michaelfsb/cea_sadv_cape_bbb/componetes/MPU-6050/3D/MPU-6050.stp

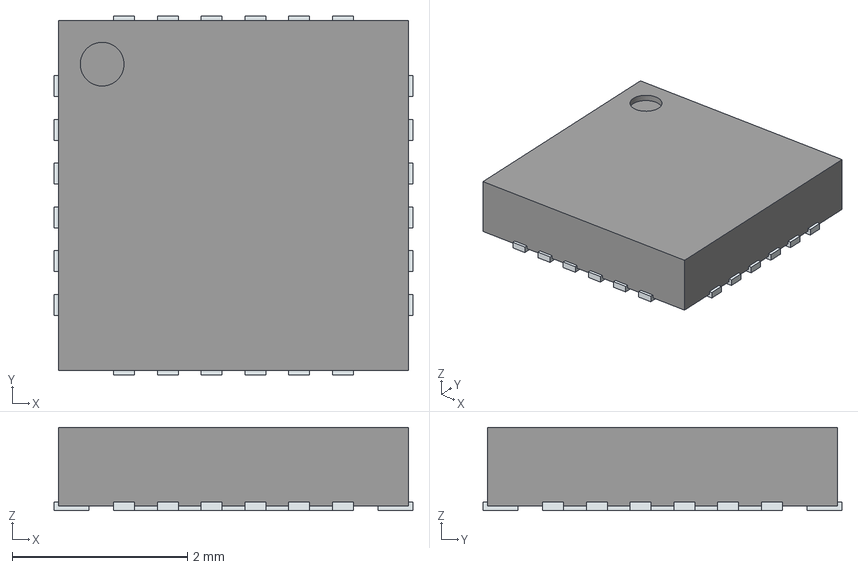
[picture p15: CAD file, 2018-07-10]
componetes/MPU-6050/3D/MPU-6050.stp
4.10 x 4.10 x 0.95 mm
ThermalPin
PinsArrayLR
PinsArrayTB
