michaelfsb/cea_sadv_cape_bbb/componetes/MPU-6500/3D/mpu6500.STEP

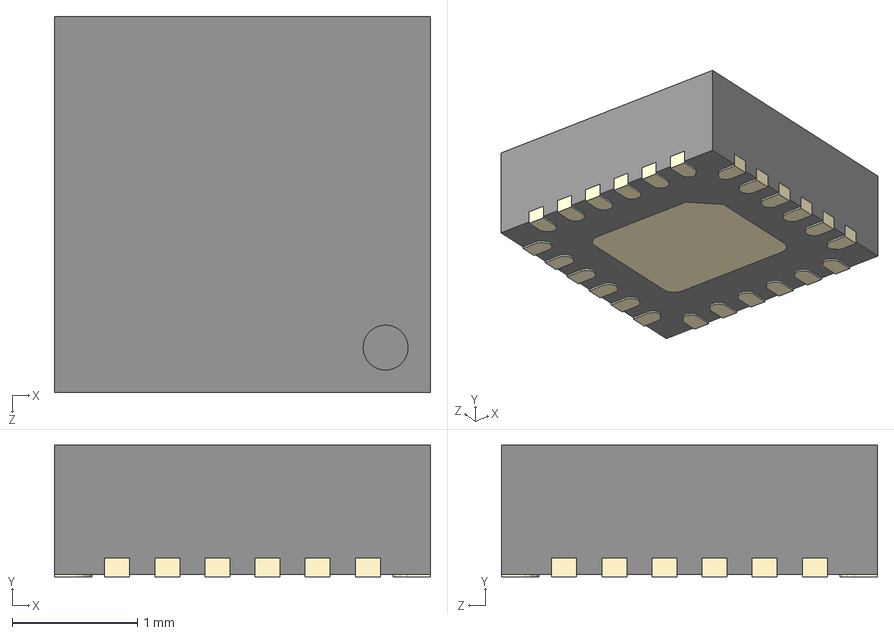
[picture p16: CAD file, 2018-08-18]
componetes/MPU-6500/3D/mpu6500.STEP
3.00 x 1.05 x 3.00 mm
