michaelfsb/cea_sadv_cape_bbb/componetes/MPU-9250/3D/MPU-9250.stp

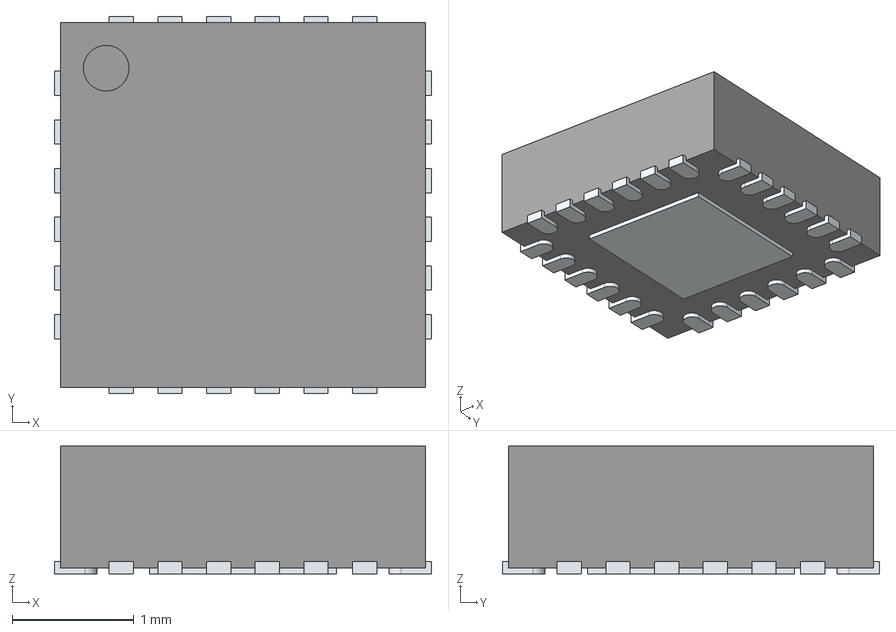
[picture p17: CAD file, 2018-07-10]
componetes/MPU-9250/3D/MPU-9250.stp
3.10 x 3.10 x 1.05 mm
ThermalPin
PinsArrayLR
PinsArrayTB
