michaelfsb/cea_sadv_cape_bbb/componetes/BMP180/bmp180-2.snapshot.1/BMP_180/PCB.SLDPRT

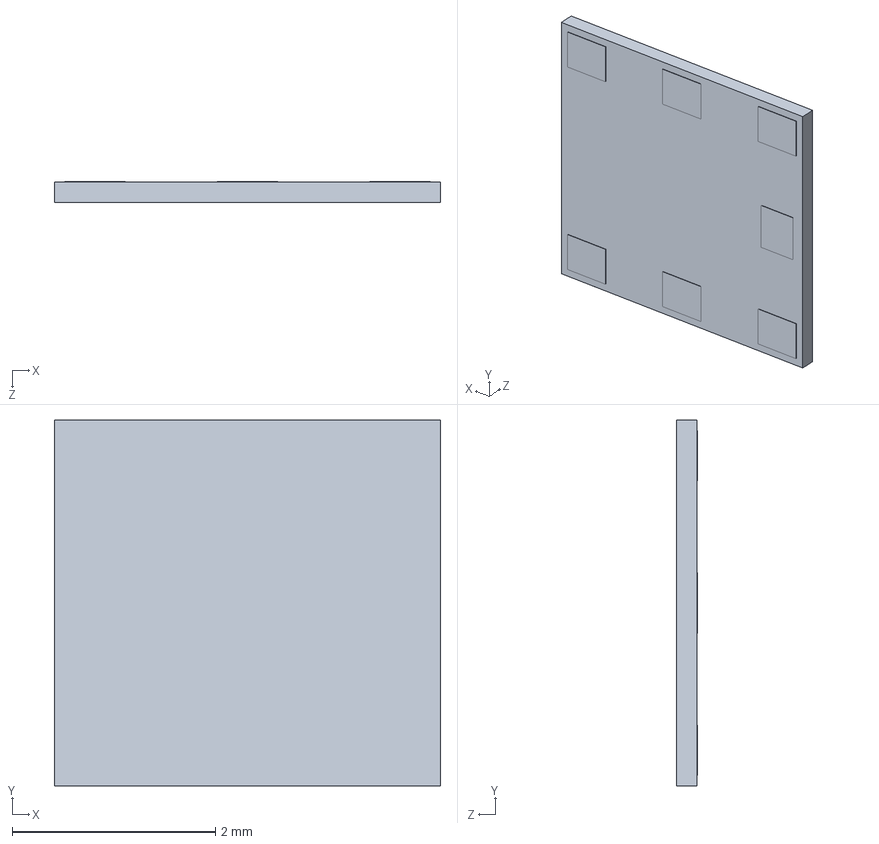
[picture p18: CAD file, 2018-08-18]
componetes/BMP180/bmp180-2.snapshot.1/BMP_180/PCB.SLDPRT
3.80 x 3.60 x 0.206 mm
